NoIDidntHackU/PHS/design/kicad/main_board/main_board.kicad_sch

## KiCad design design/kicad/main_board/main_board.kicad_sch (2023-10-20)

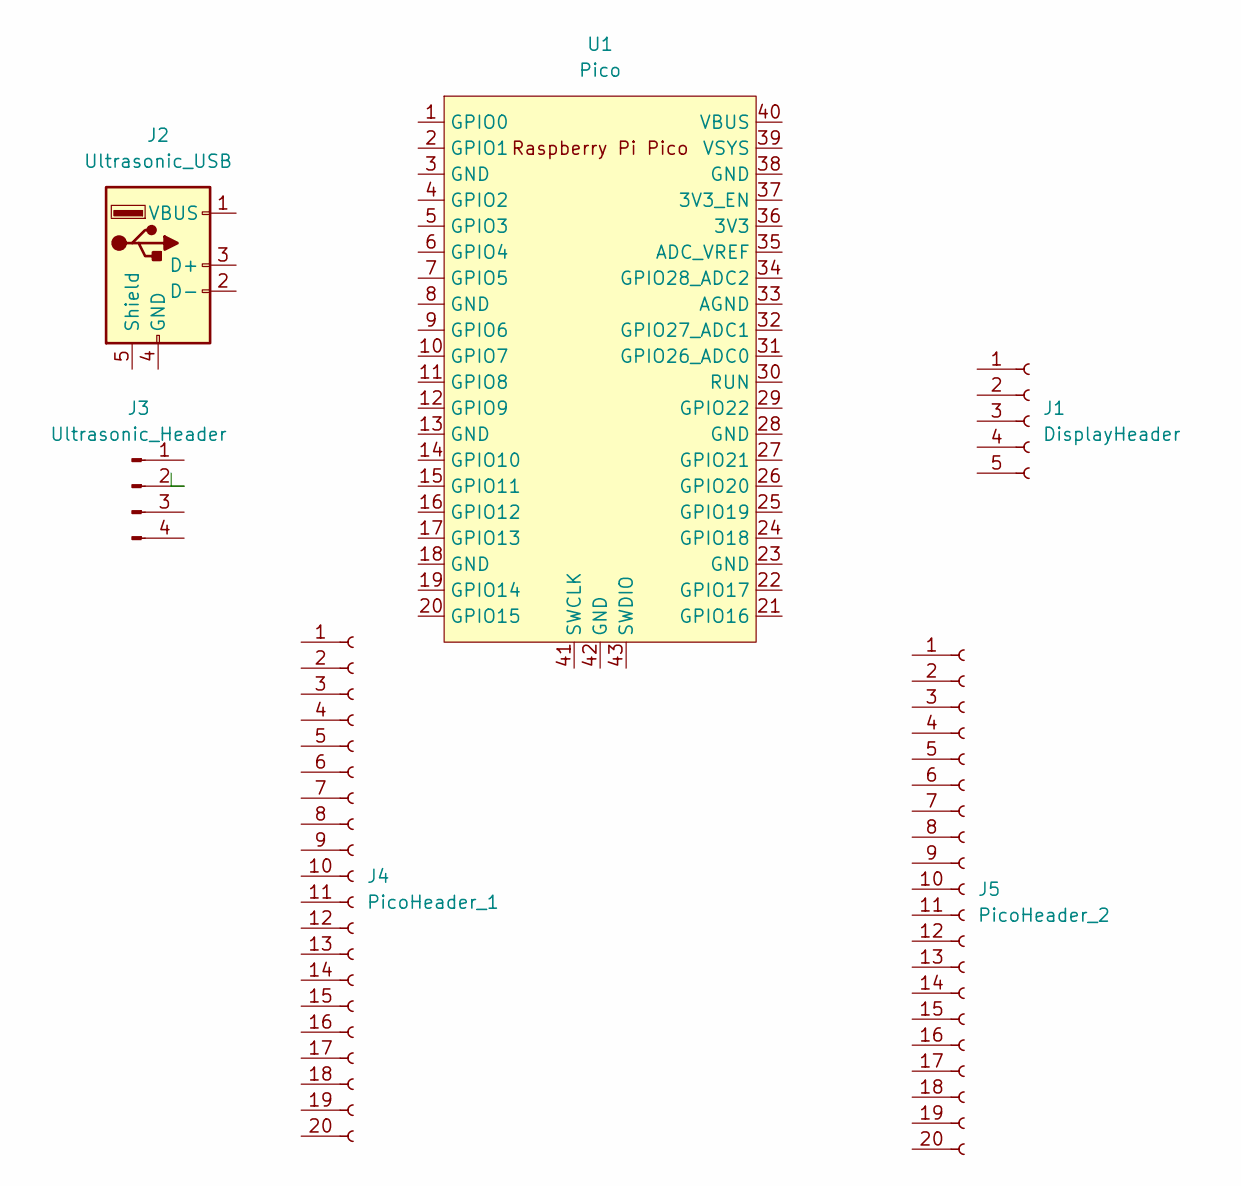
[picture p6: schematic main_board.kicad_sch]

Parts:
J1: DisplayHeader; PinHeader_1x05_P2.54mm_Vertical
J2: Ultrasonic_USB; USB_A_Molex_67643_Horizontal
J3: Ultrasonic_Header; PinHeader_1x04_P2.54mm_Vertical
J4: PicoHeader_1; PinHeader_1x20_P2.54mm_Vertical
J5: PicoHeader_2; PinHeader_1x20_P2.54mm_Vertical
U1: Pico; RPi_Pico_SMD_TH
